prilosac/ErgoDashEnclosedCase/dxfs/mini/minirightbordertopx1.dxf

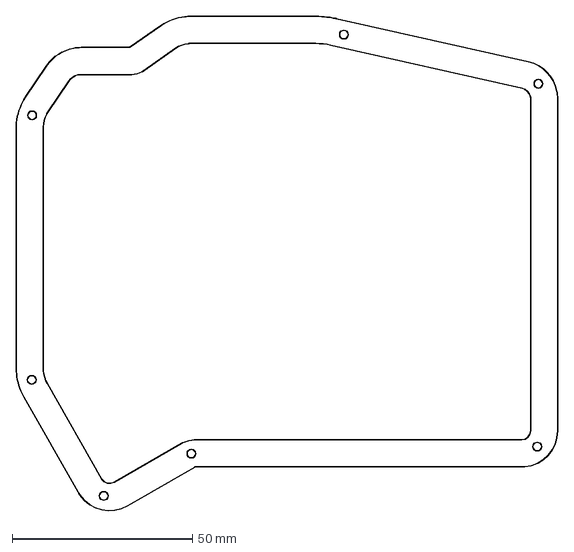
[picture p28: CAD file, 2025-08-23]
dxfs/mini/minirightbordertopx1.dxf
150.1 x 137.3 mm
