prilosac/ErgoDashEnclosedCase/dxfs/full/rightbottomx1.dxf

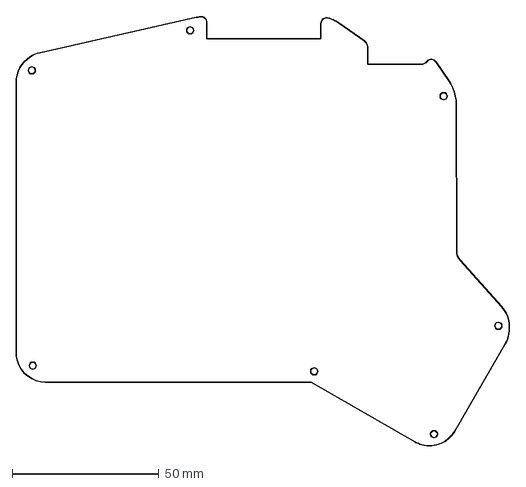
[picture p29: CAD file, 2025-08-23]
dxfs/full/rightbottomx1.dxf
168.3 x 146.6 mm
