prilosac/ErgoDashEnclosedCase/dxfs/mini/minirightborderx2.dxf

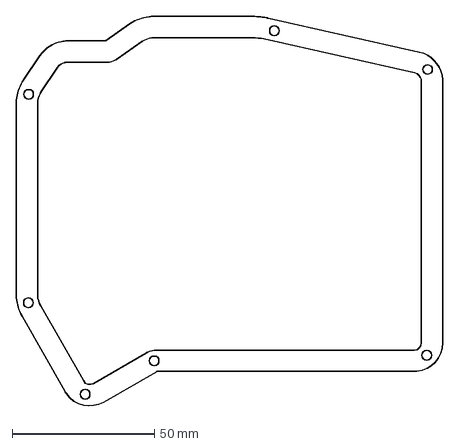
[picture p30: CAD file, 2025-08-23]
dxfs/mini/minirightborderx2.dxf
150.1 x 137.3 mm
