prilosac/ErgoDashEnclosedCase/dxfs/full/leftbottomcutoutx1.dxf

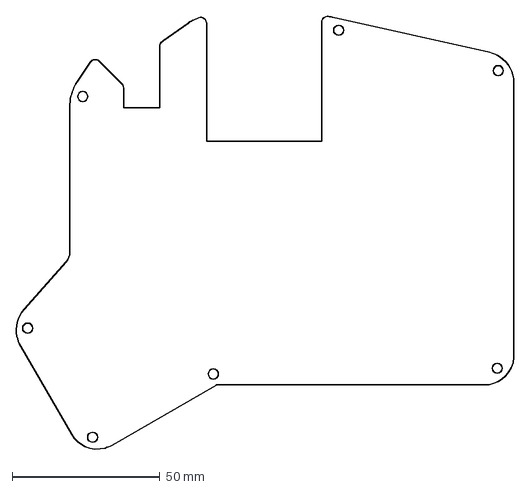
[picture p31: CAD file, 2025-08-23]
dxfs/full/leftbottomcutoutx1.dxf
168.3 x 146.6 mm
