prilosac/ErgoDashEnclosedCase/dxfs/mini/minirightbottomx1.dxf

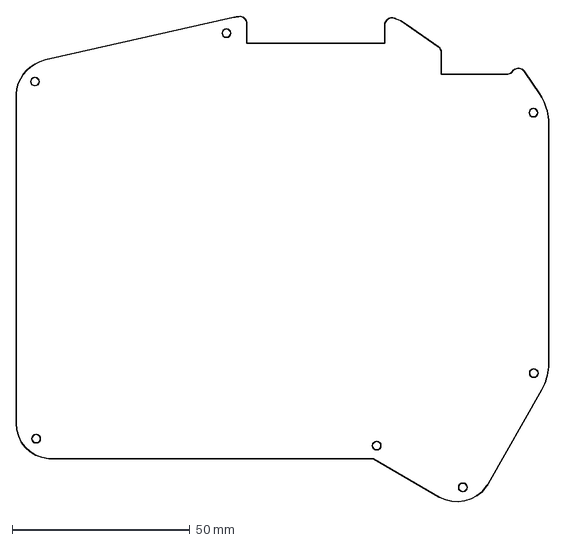
[picture p32: CAD file, 2025-08-23]
dxfs/mini/minirightbottomx1.dxf
150.1 x 137.0 mm
