prilosac/ErgoDashEnclosedCase/dxfs/full/leftbordertopx1.dxf

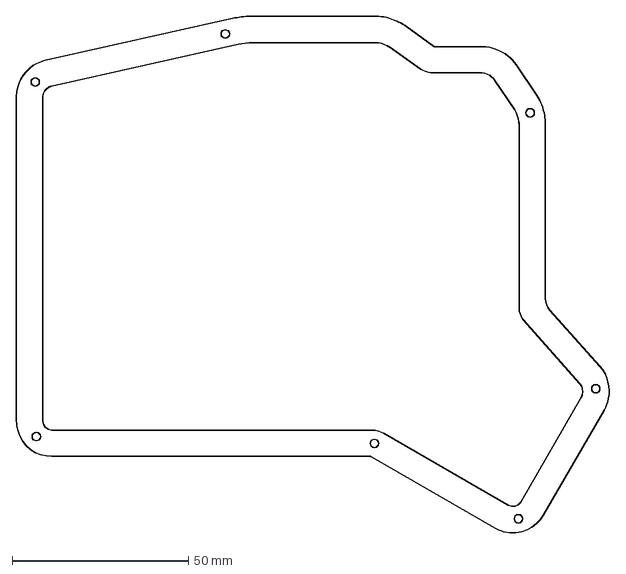
[picture p33: CAD file, 2025-08-23]
dxfs/full/leftbordertopx1.dxf
168.3 x 146.9 mm
