prilosac/ErgoDashEnclosedCase/dxfs/mini/minileftbottomcutoutx1.dxf

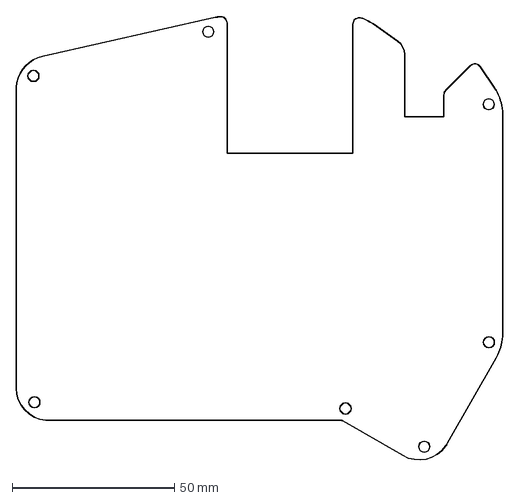
[picture p34: CAD file, 2025-08-23]
dxfs/mini/minileftbottomcutoutx1.dxf
150.1 x 137.0 mm
