prilosac/ErgoDashEnclosedCase/dxfs/full/leftbottomx1.dxf

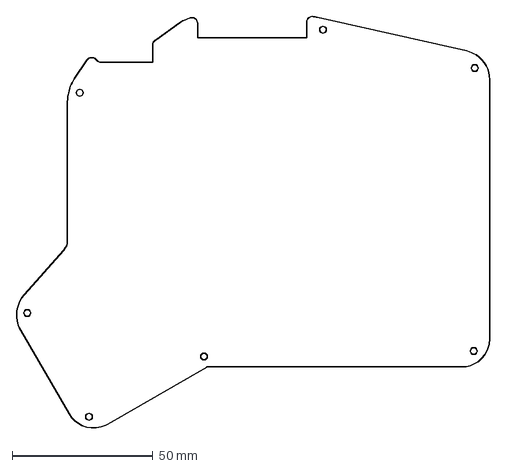
[picture p35: CAD file, 2025-08-23]
dxfs/full/leftbottomx1.dxf
168.3 x 146.6 mm
