prilosac/ErgoDashEnclosedCase/dxfs/mini/minileftbottomx1.dxf

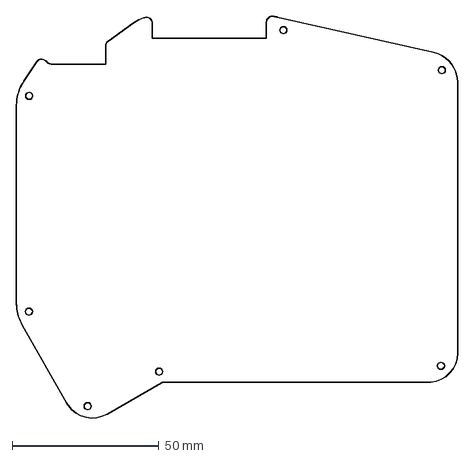
[picture p36: CAD file, 2025-08-23]
dxfs/mini/minileftbottomx1.dxf
150.1 x 137.0 mm
