prilosac/ErgoDashEnclosedCase/dxfs/full/rightbordercutoutx2.dxf

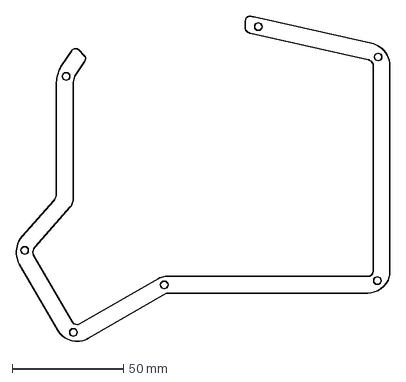
[picture p37: CAD file, 2025-08-23]
dxfs/full/rightbordercutoutx2.dxf
168.3 x 146.6 mm
