prilosac/ErgoDashEnclosedCase/dxfs/mini/minirightbottomcutoutx1.dxf

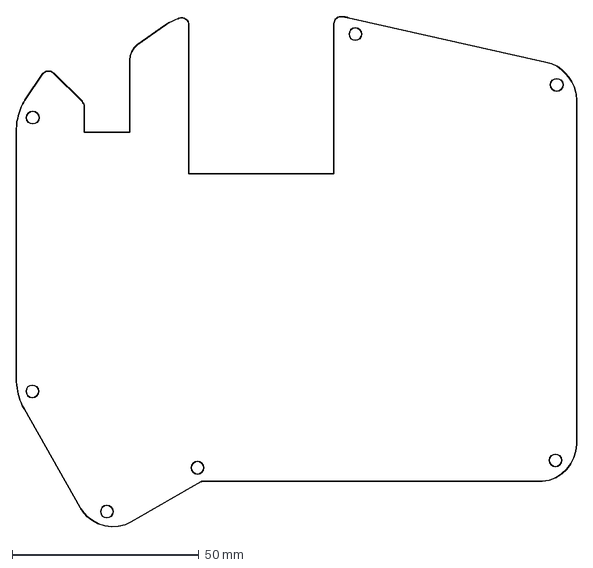
[picture p38: CAD file, 2025-08-23]
dxfs/mini/minirightbottomcutoutx1.dxf
150.1 x 137.0 mm
